jdc-cunningham/fusion-sensor-clu/repo-images/cam-sees-at-3-ft.PNG

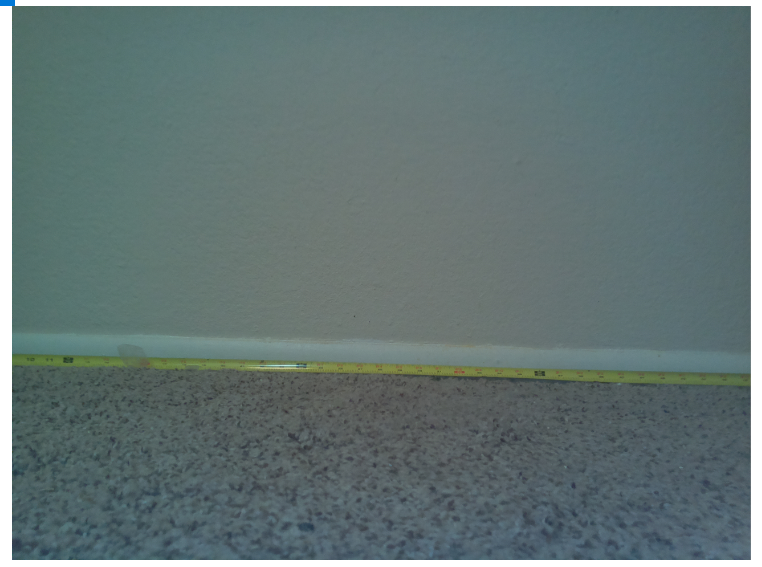
repo-images/cam-sees-at-3-ft.PNG
