jdc-cunningham/fusion-sensor-clu/3dfiles/stl/tilt-base.stl

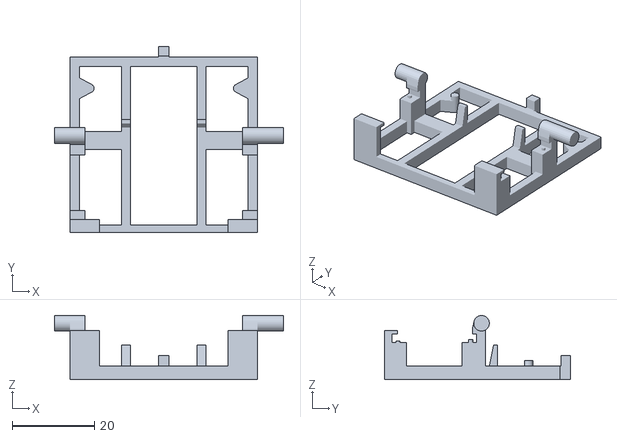
[picture p44: CAD file, 2020-10-29]
3dfiles/stl/tilt-base.stl
55.6 x 45.0 x 15.5
