jdc-cunningham/fusion-sensor-clu/3dfiles/stl/stepper-pan-tilt.stl

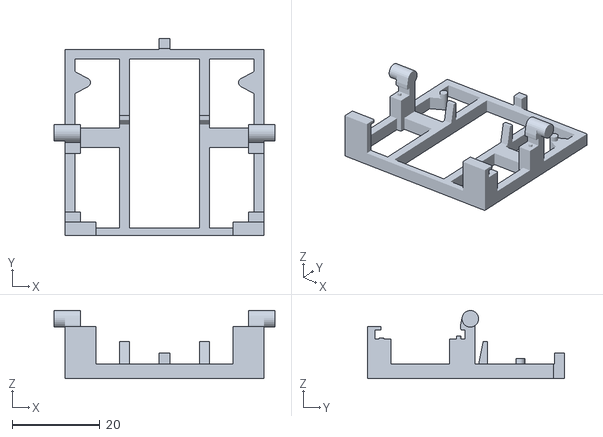
[picture p45: CAD file, 2020-10-29]
3dfiles/stl/stepper-pan-tilt.stl
50.5 x 45.0 x 15.5
