jdc-cunningham/fusion-sensor-clu/3dfiles/stl/pan-tilt-axes.stl

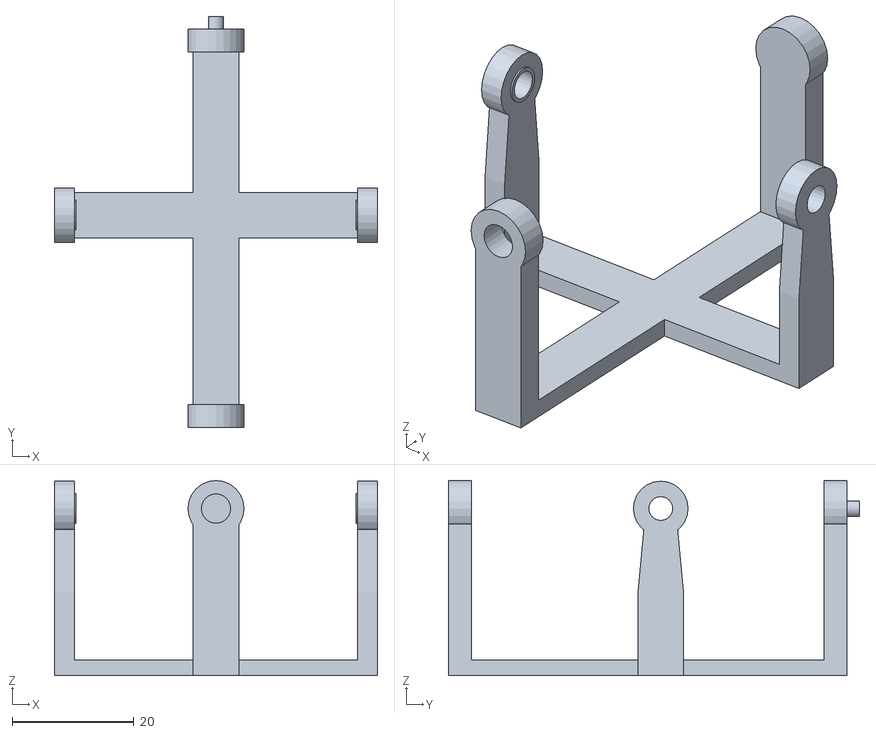
[picture p46: CAD file, 2020-10-29]
3dfiles/stl/pan-tilt-axes.stl
53.0 x 67.4 x 32.0
