jdc-cunningham/fusion-sensor-clu/vision/testing/output-images/mask-applied.jpg

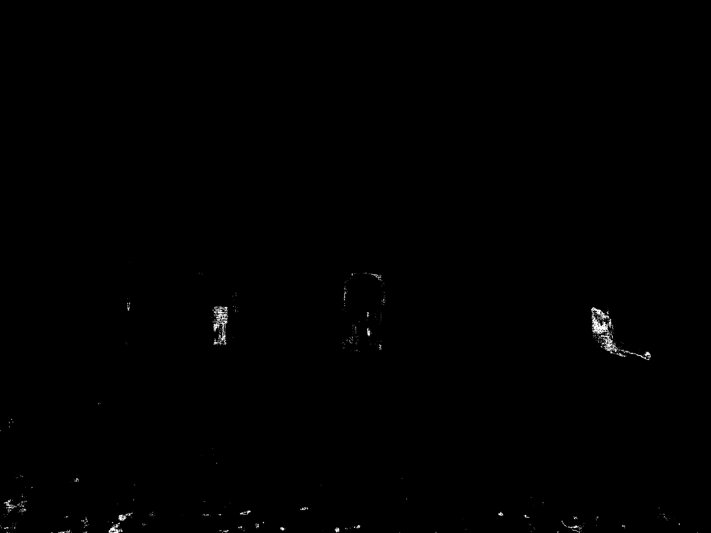
vision/testing/output-images/mask-applied.jpg
