jdc-cunningham/fusion-sensor-clu/vision/testing/sample-images/test_light.jpg

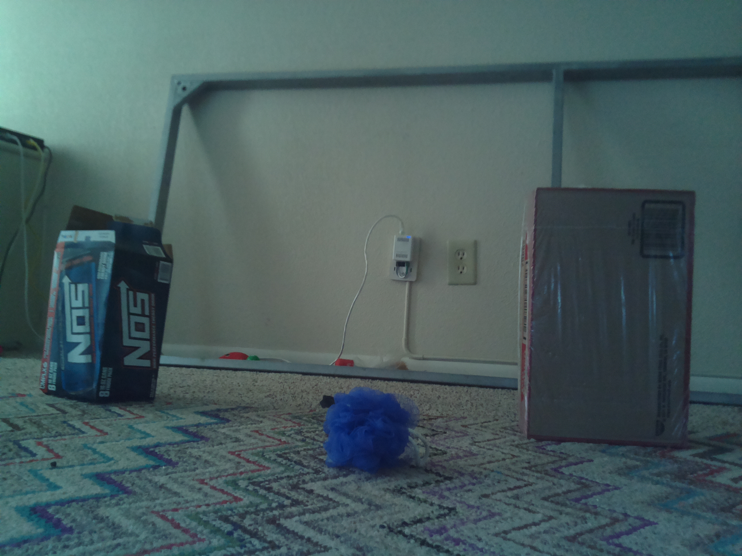
vision/testing/sample-images/test_light.jpg
