jdc-cunningham/fusion-sensor-clu/pi/system/camera.py

# data depicted here is for 5MP 1080P Pi Camera
# viewing angle 72 degrees
# max resolution: 2592 x 1944
# 1080p @ 30fps
# 720p @ 60fps
# 640x480p 60/90 fps recording
# angle of view 50deg x 41deg
# fixed focus 1m - infinity
# about lens
# FoV 2x1.33 m at 2m
# angle of view 54 x 41 deg
# focal length 3.6mm
# https://www.arducam.com/product/arducam-ov5647-standard-raspberry-pi-camera-b0033/
# https://www.raspberrypi.org/forums/viewtopic.php?t=150344

class Camera:
  def __init__(self):
